hmatt1/pcb-100mm-slider-i2c/adafruit-sliders.png

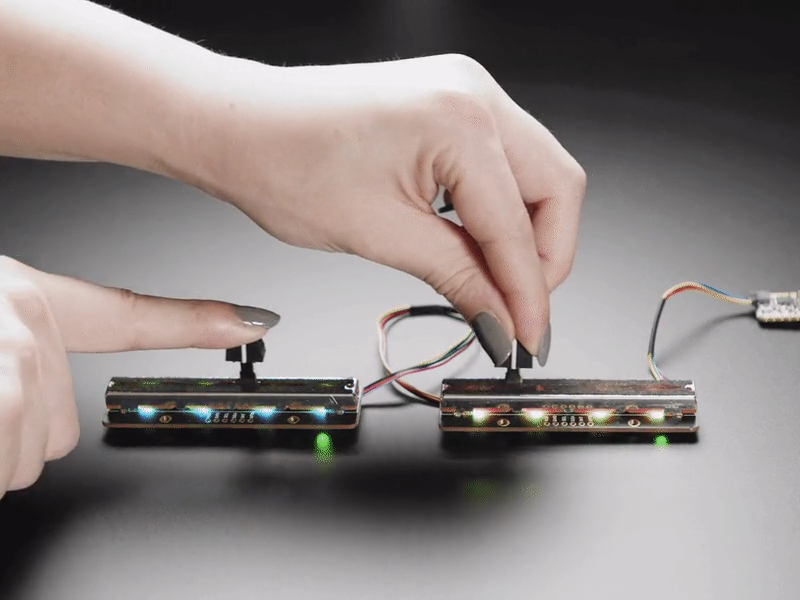
adafruit-sliders.png
