hmatt1/pcb-100mm-slider-i2c/assets-webp/511ac8f5ce395f5846000000.webp

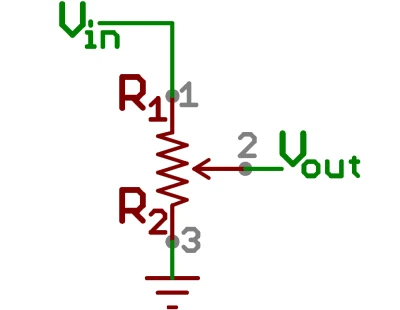
assets-webp/511ac8f5ce395f5846000000.webp
