hmatt1/pcb-100mm-slider-i2c/assets-webp/bourns voltage div.webp

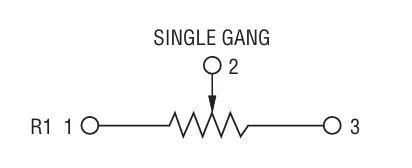
assets-webp/bourns voltage div.webp
