hmatt1/pcb-100mm-slider-i2c/assets-webp/IMG_1569.webp

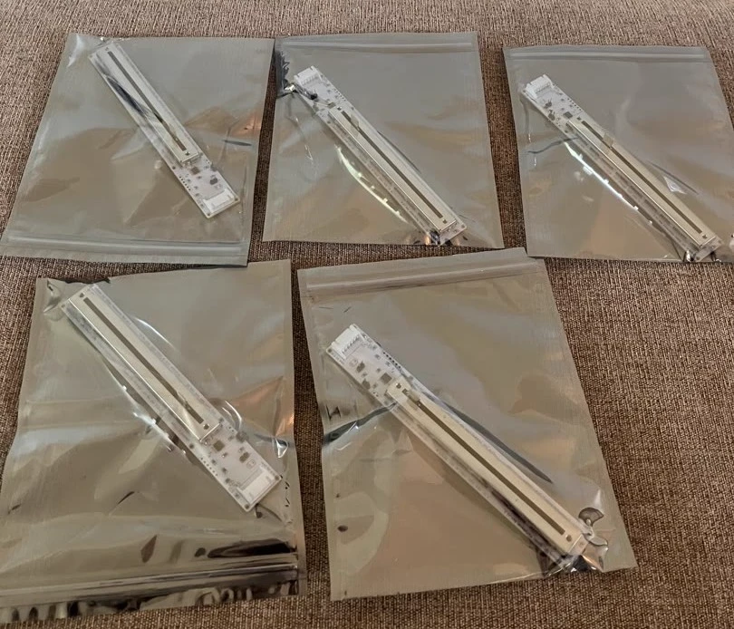
assets-webp/IMG_1569.webp
