hmatt1/pcb-100mm-slider-i2c/assets-webp/potentiometer-symbol-2.webp

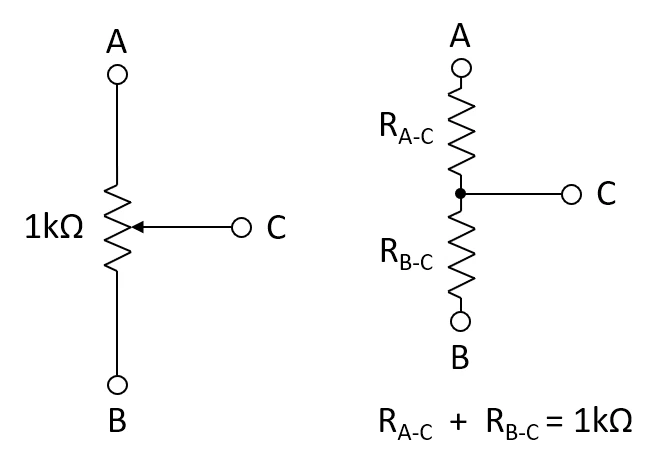
assets-webp/potentiometer-symbol-2.webp
