hmatt1/pcb-100mm-slider-i2c/photos/IMG_0046_Video_3.png

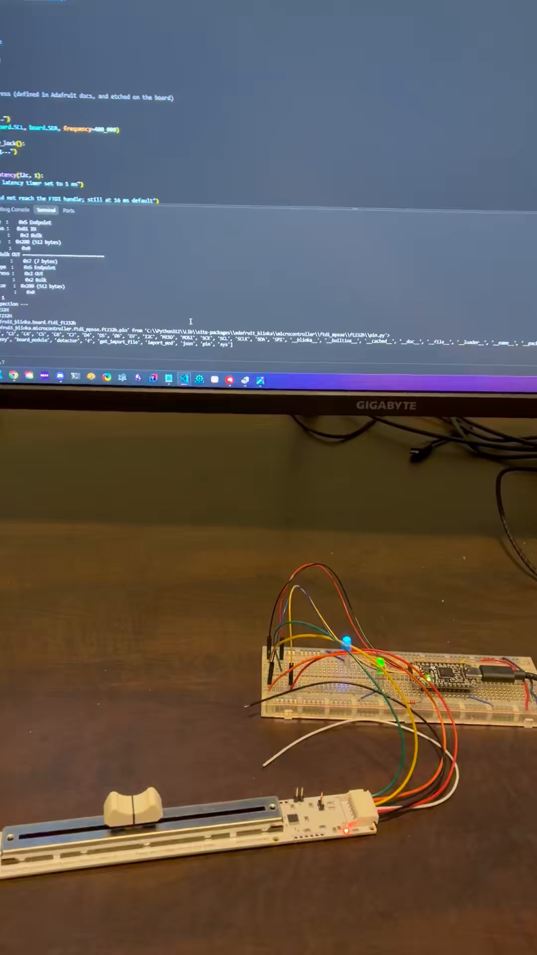
photos/IMG_0046_Video_3.png
