hmatt1/pcb-100mm-slider-i2c/photos/IMG_1269.webp

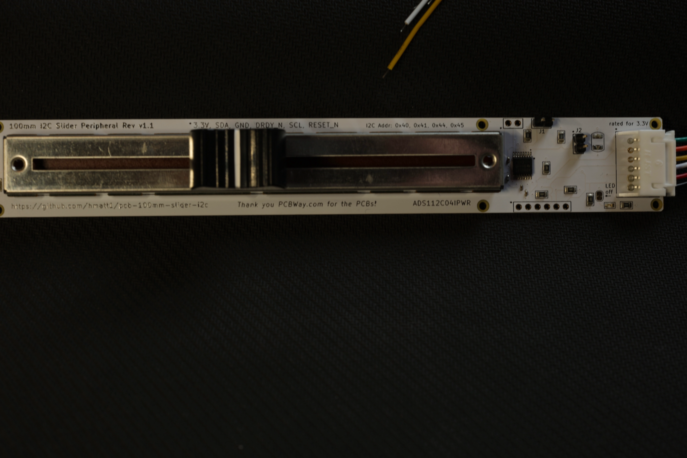
photos/IMG_1269.webp
