hmatt1/pcb-100mm-slider-i2c/photos/IMG_1269_1.webp

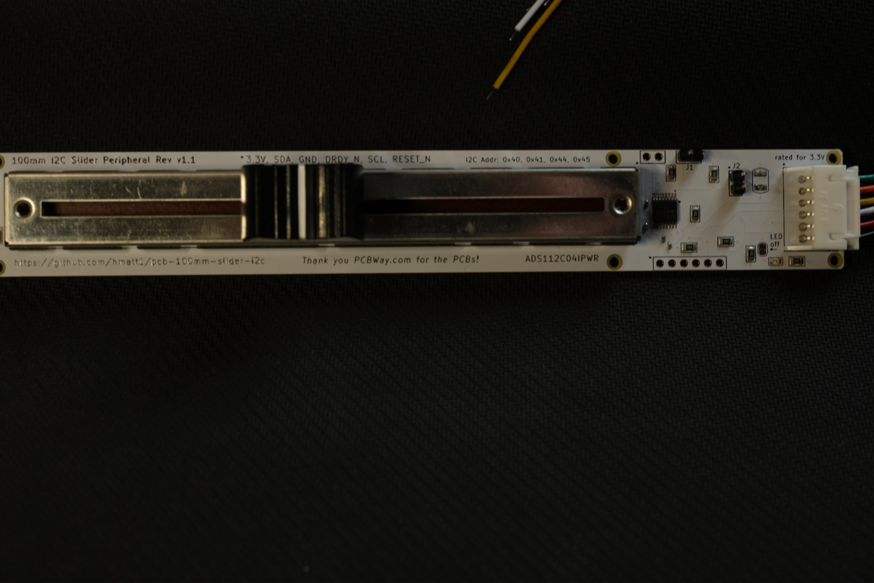
photos/IMG_1269_1.webp
