hmatt1/pcb-100mm-slider-i2c/photos/IMG_1272.JPG

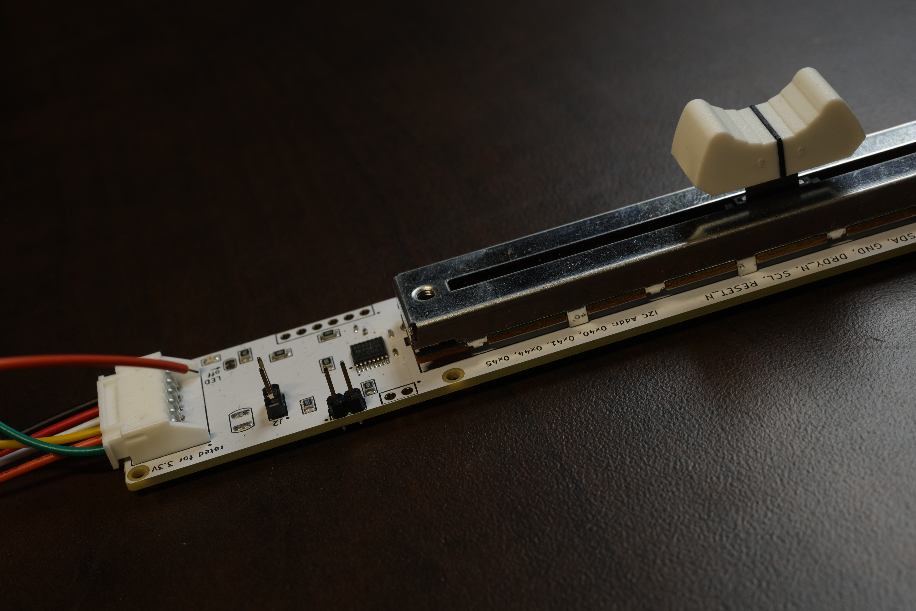
photos/IMG_1272.JPG
